tomtebloss/MV16/Pics/9_PCB_top.png

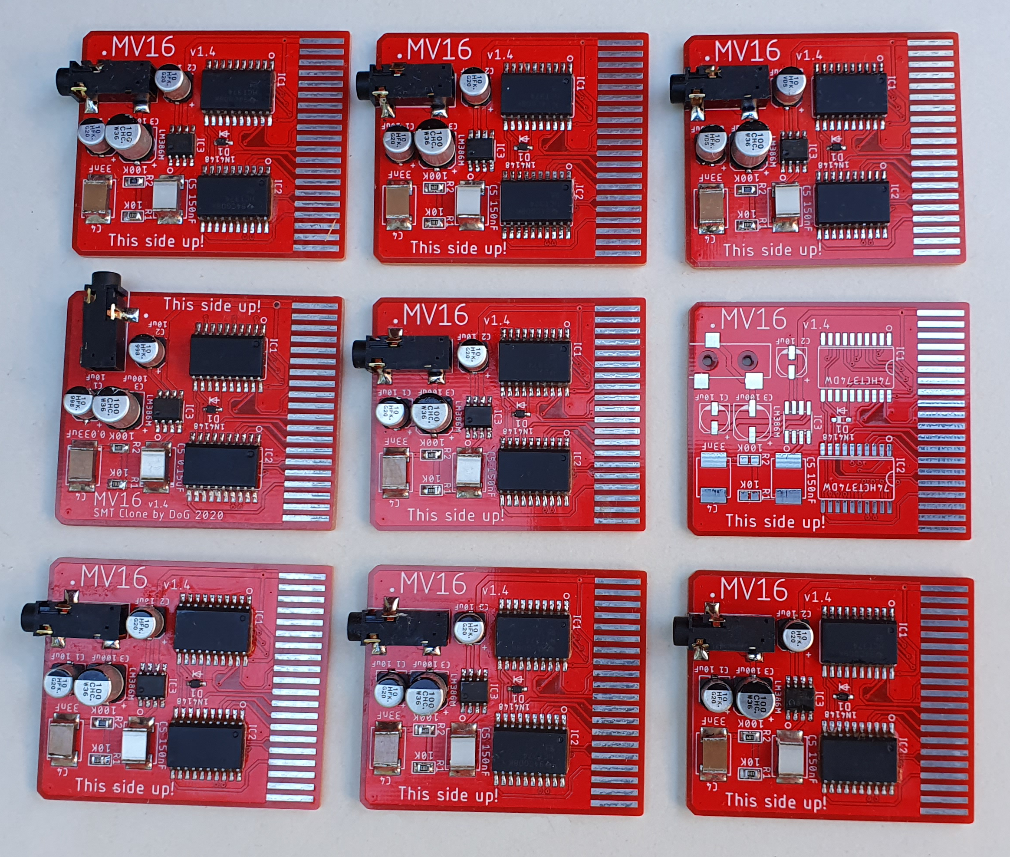
Pics/9_PCB_top.png
