tomtebloss/MV16/Pics/Box_1.jpg

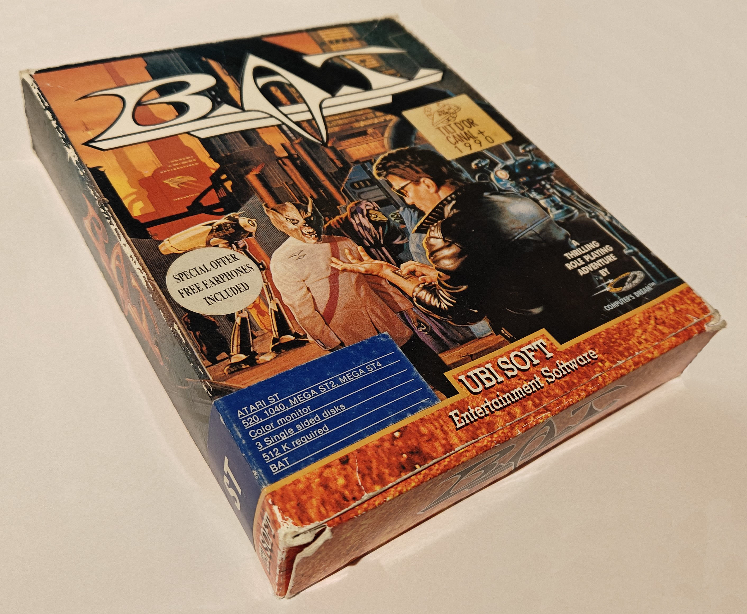
Pics/Box_1.jpg
