tomtebloss/MV16/Pics/MV16 v1.4.jpg

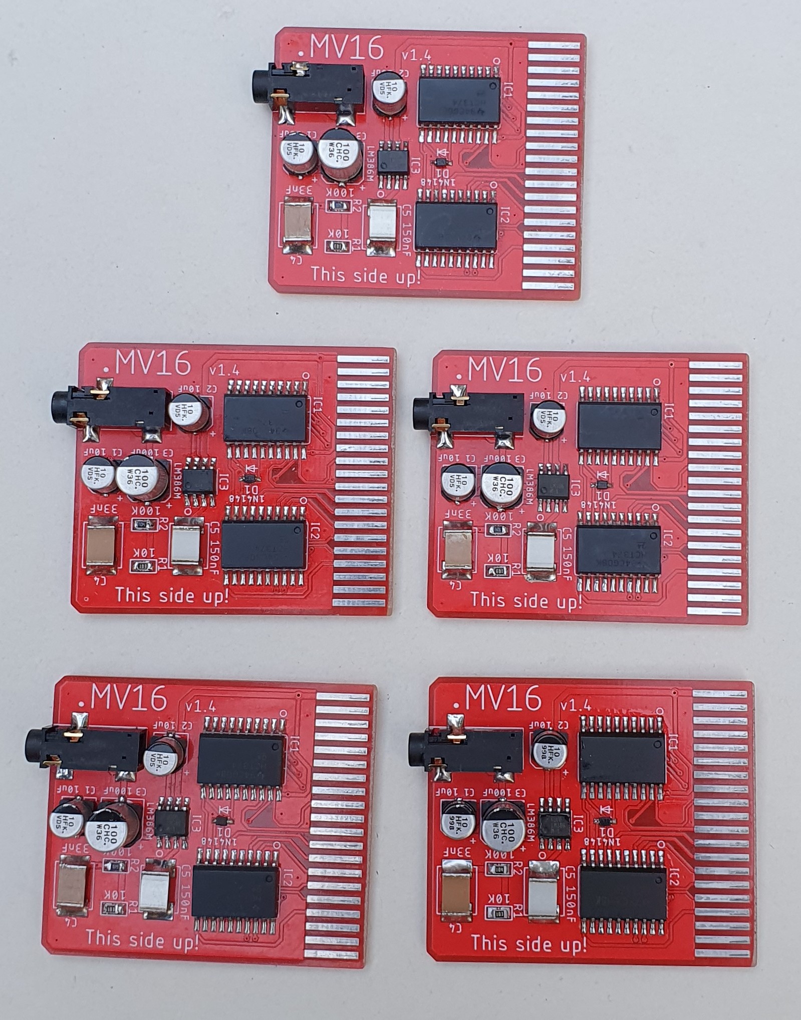
Pics/MV16 v1.4.jpg
