tomtebloss/MV16/Pics/MV16_layout_bottom.png

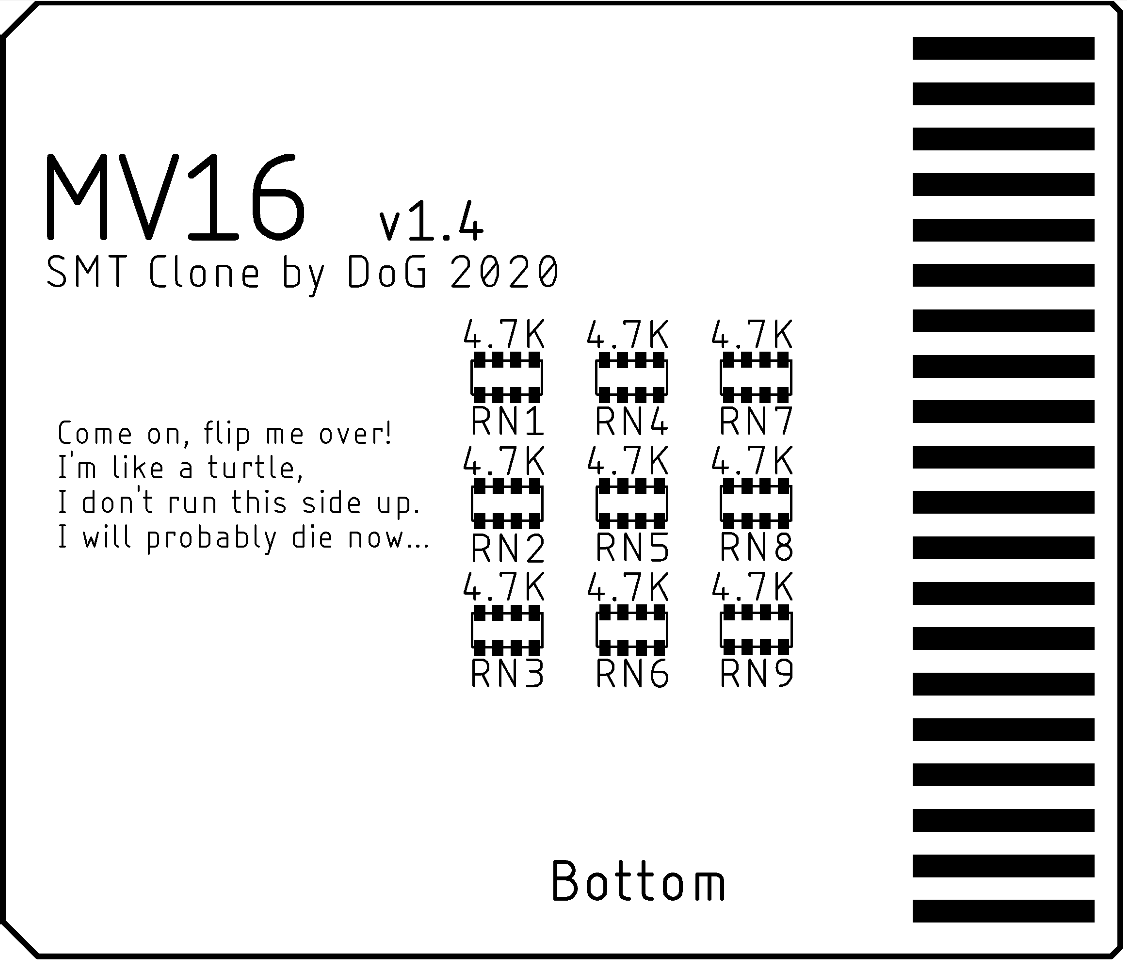
Pics/MV16_layout_bottom.png
