tomtebloss/MV16/Pics/original_cart_components.jpg

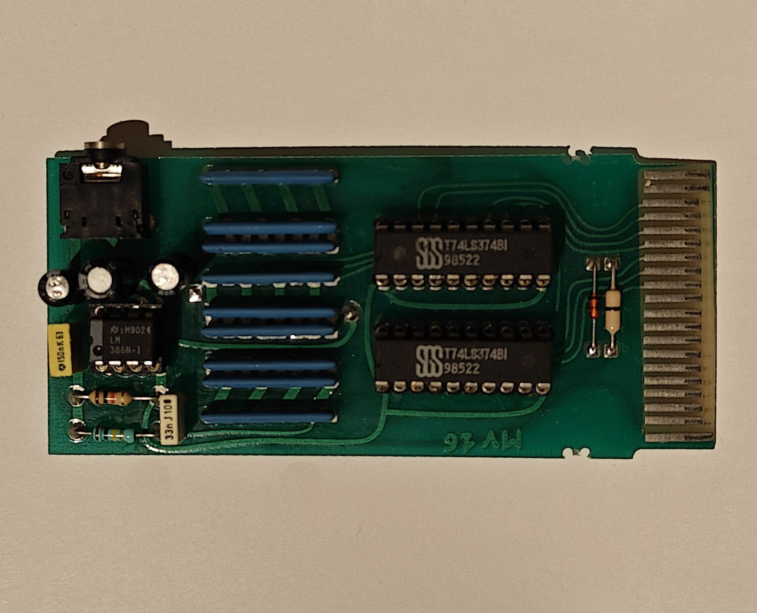
Pics/original_cart_components.jpg
