tomtebloss/MV16/Pics/Atari_manual.jpg

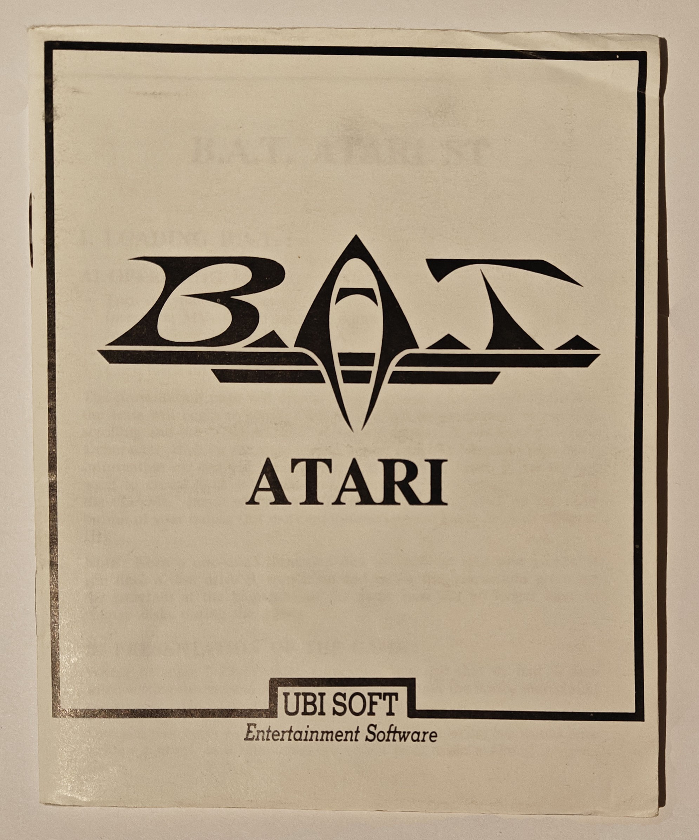
Pics/Atari_manual.jpg
