tomtebloss/MV16/Pics/Manual_and_story.jpg

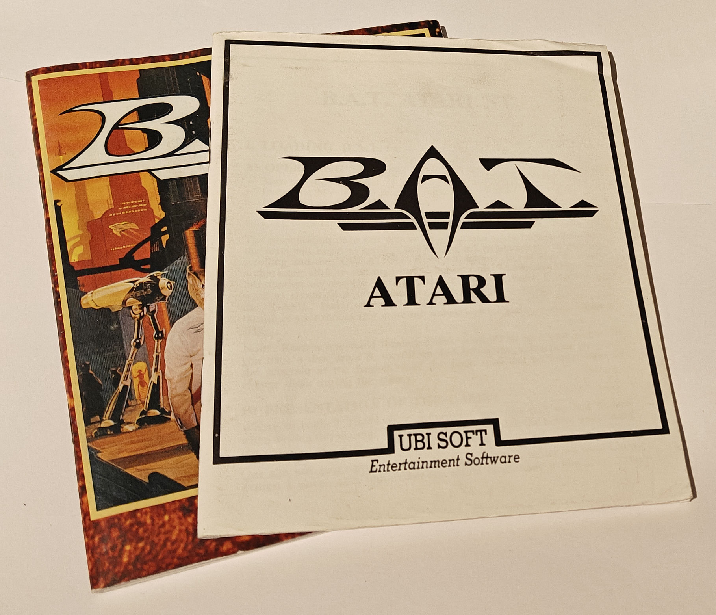
Pics/Manual_and_story.jpg
